CyZooNiC/cyberdeck/photos/P_20210604_110600.jpg

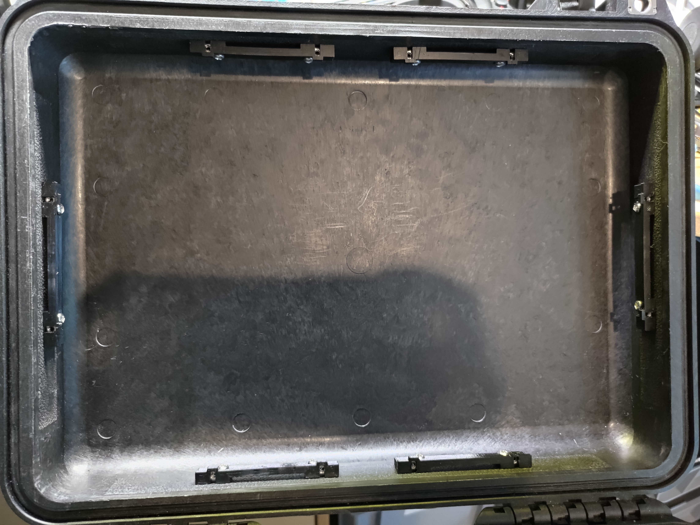
photos/P_20210604_110600.jpg
