CyZooNiC/cyberdeck/photos/P_20210610_104830_-_Copy.jpg

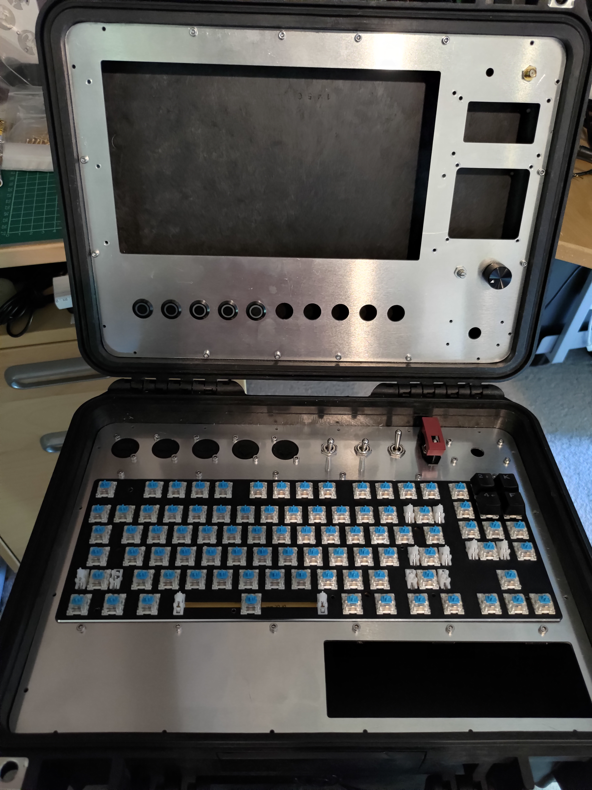
photos/P_20210610_104830_-_Copy.jpg
