CyZooNiC/cyberdeck/photos/P_20211003_194509.jpg

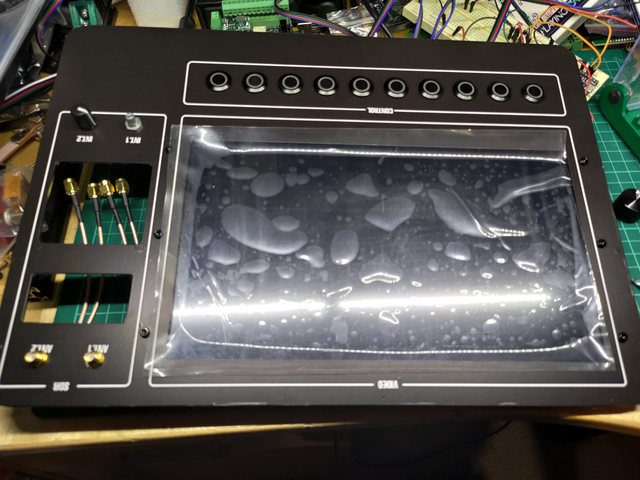
photos/P_20211003_194509.jpg
