CyZooNiC/cyberdeck/photos/P_20220129_154814.jpg

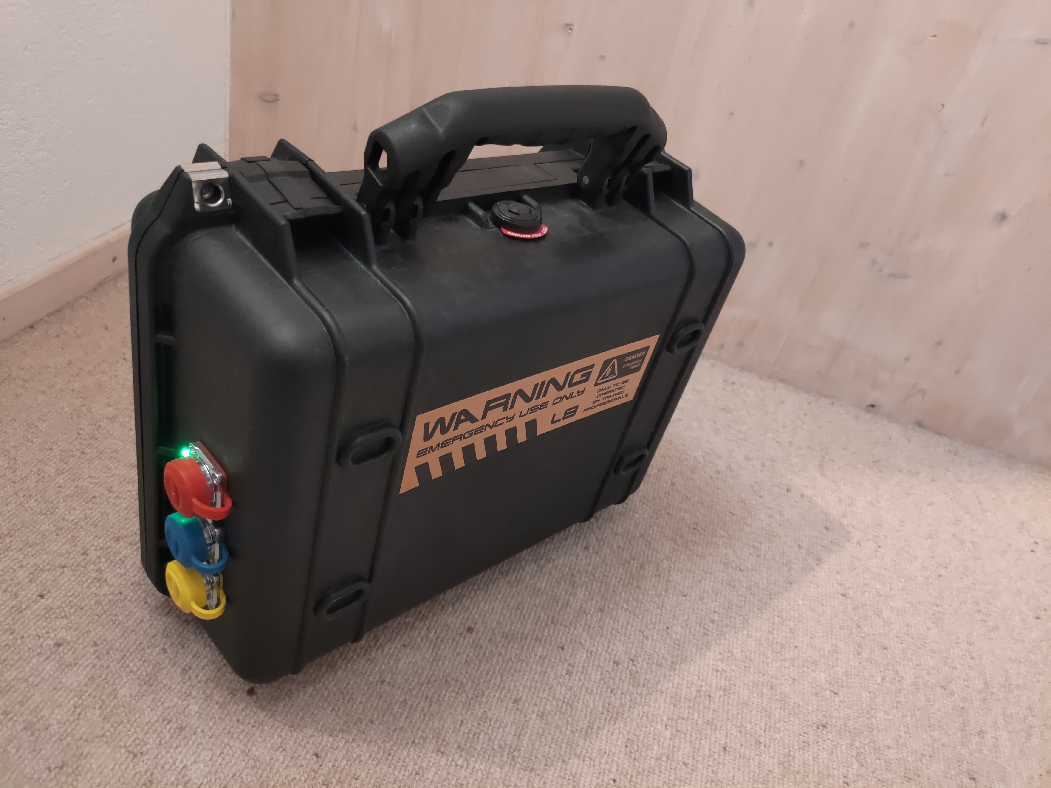
photos/P_20220129_154814.jpg
