CyZooNiC/cyberdeck/photos/P_20220129_154857.jpg

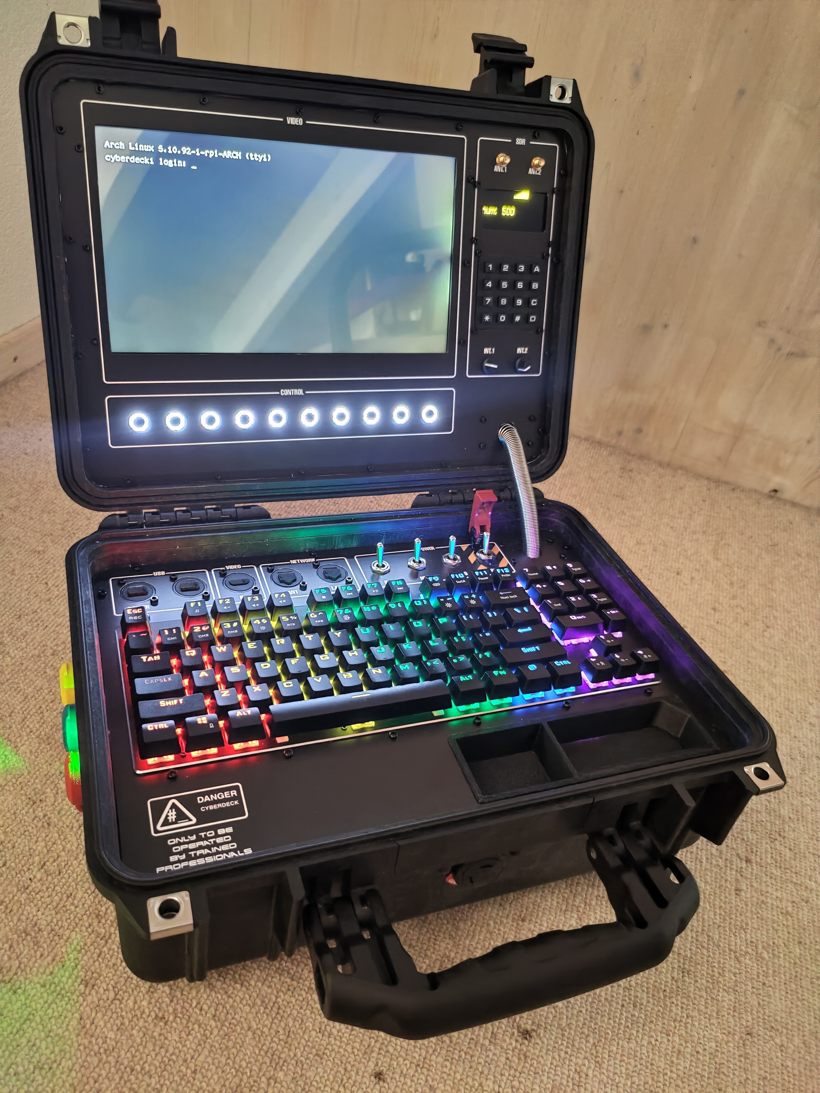
photos/P_20220129_154857.jpg
