CyZooNiC/cyberdeck/photos/P_20220129_154932.jpg

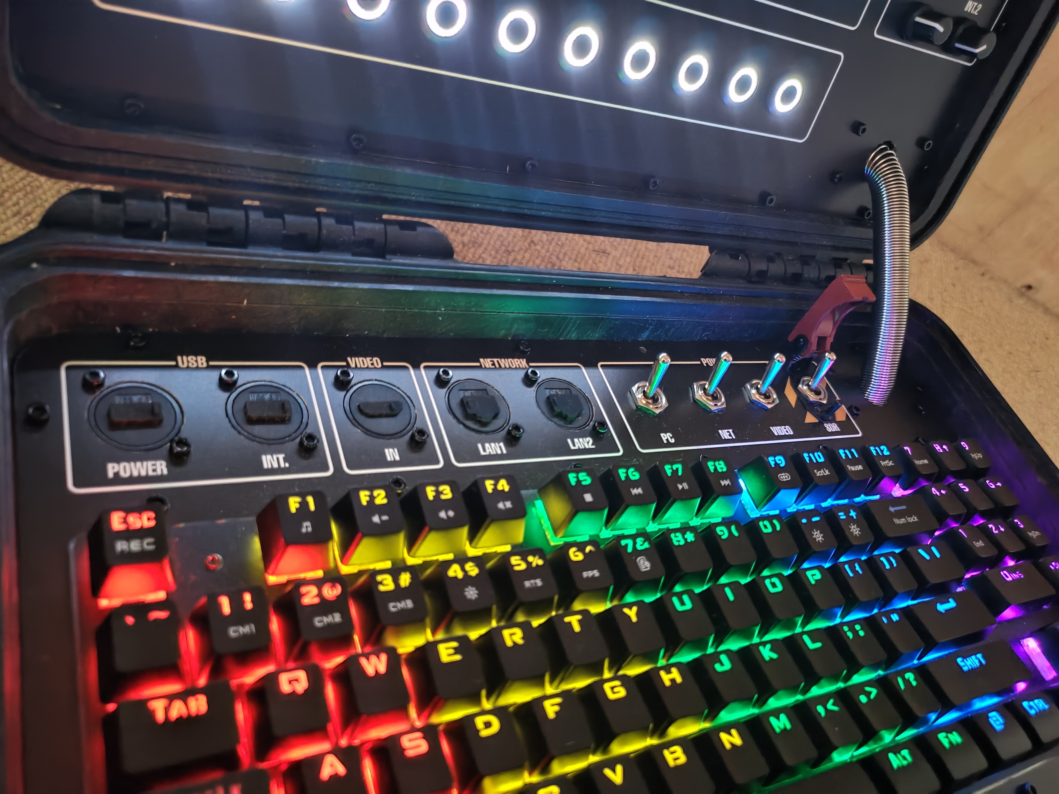
photos/P_20220129_154932.jpg
