CyZooNiC/cyberdeck/photos/P_20220129_154947.jpg

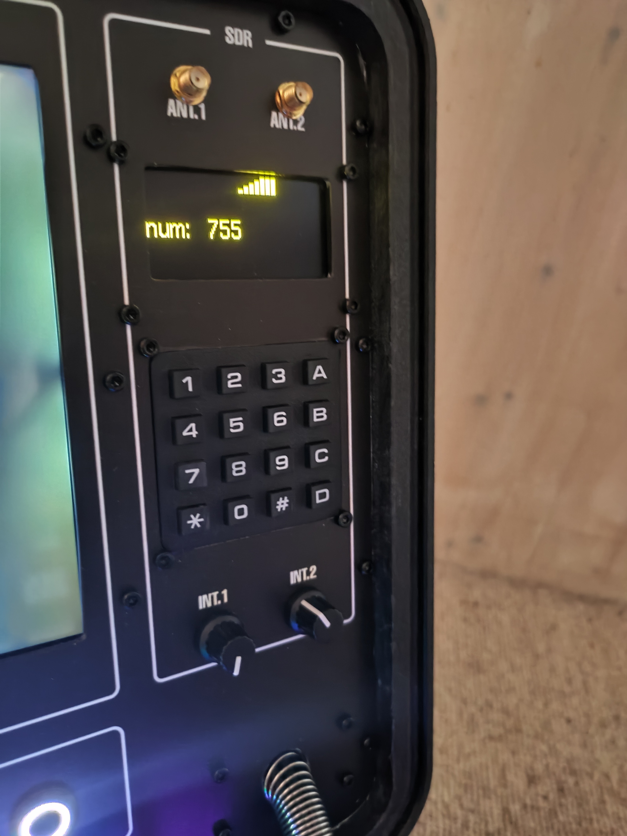
photos/P_20220129_154947.jpg
