CyZooNiC/cyberdeck/photos/P_20220129_155039.jpg

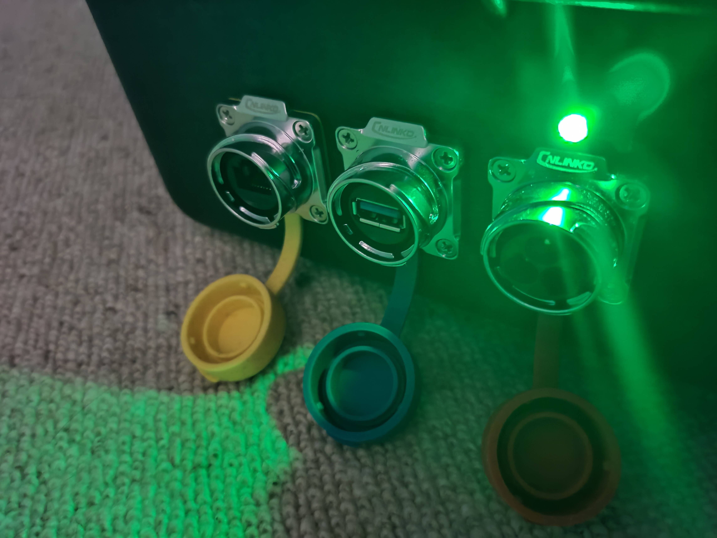
photos/P_20220129_155039.jpg
