CyZooNiC/cyberdeck/photos/P_20220129_155115.jpg

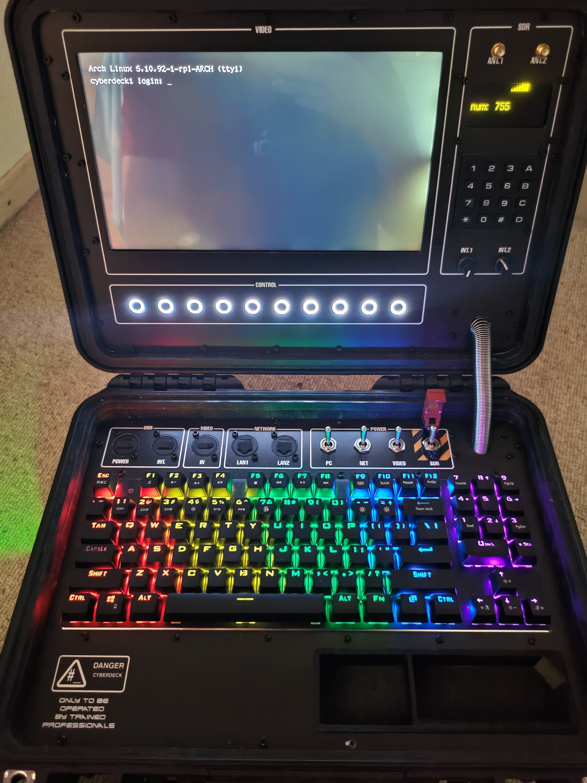
photos/P_20220129_155115.jpg
