CyZooNiC/cyberdeck/photos/P_20220205_175429.jpg

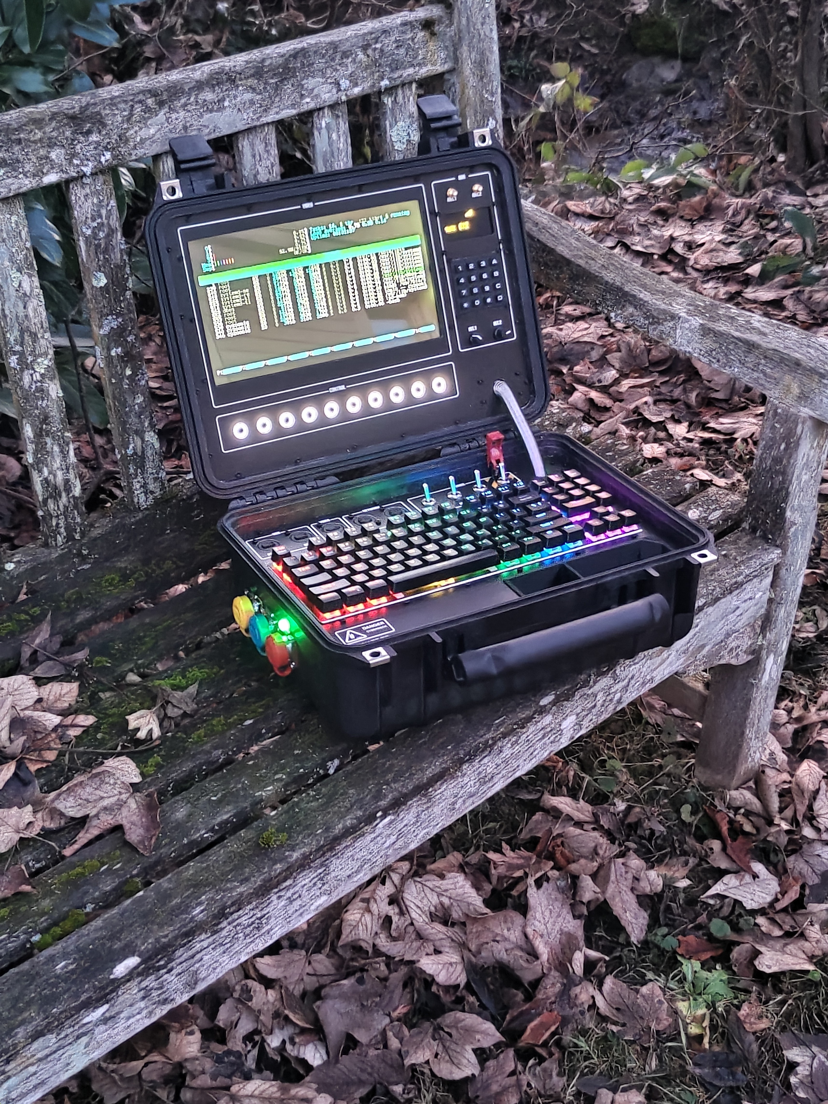
photos/P_20220205_175429.jpg
