CyZooNiC/cyberdeck/photos/P_20220205_175459.jpg

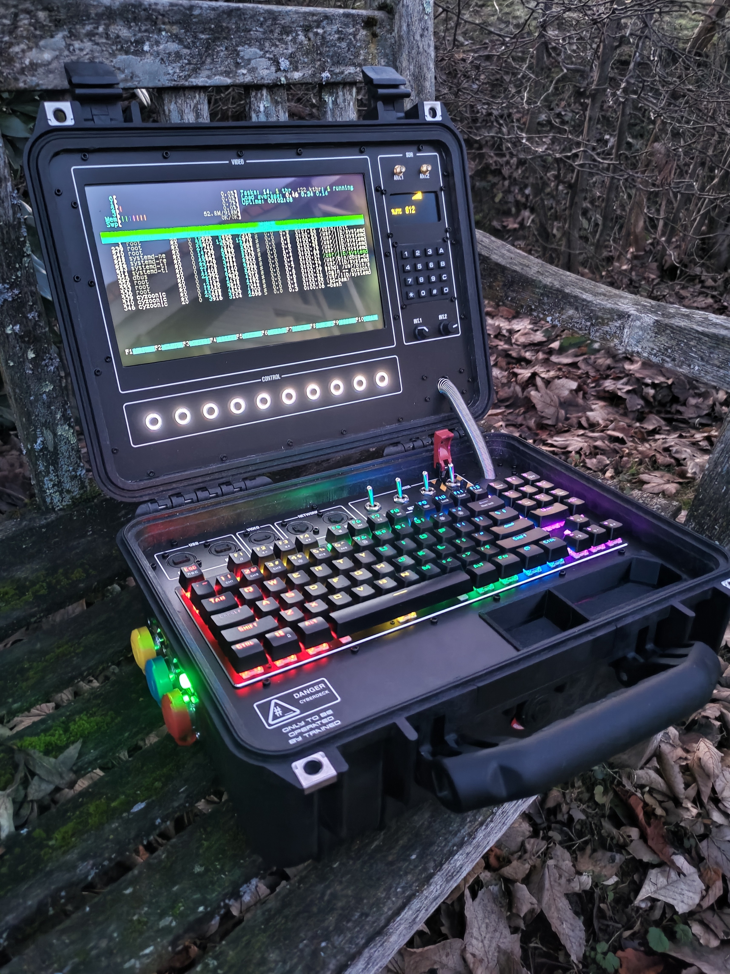
photos/P_20220205_175459.jpg
