CyZooNiC/cyberdeck/photos/P_20220205_175647.jpg

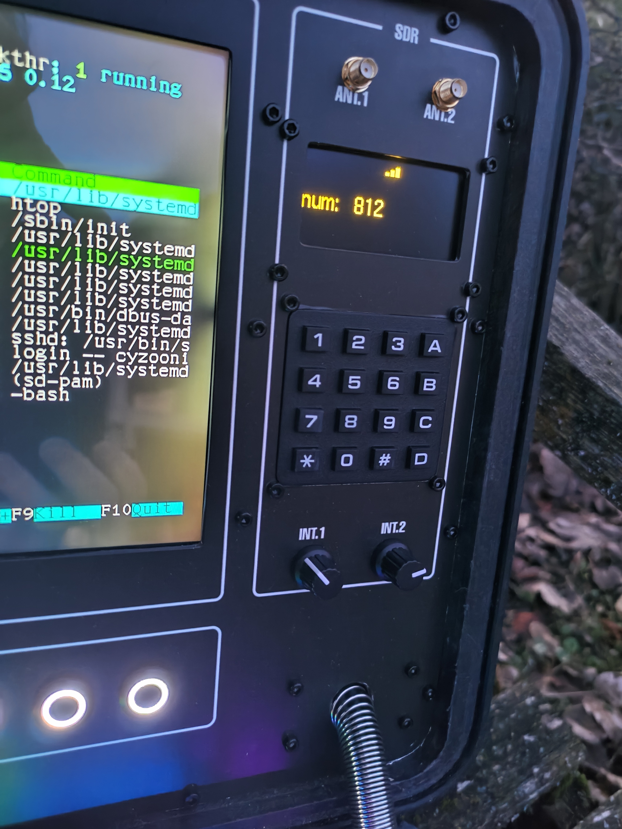
photos/P_20220205_175647.jpg
