CyZooNiC/cyberdeck/photos/P_20220205_175659.jpg

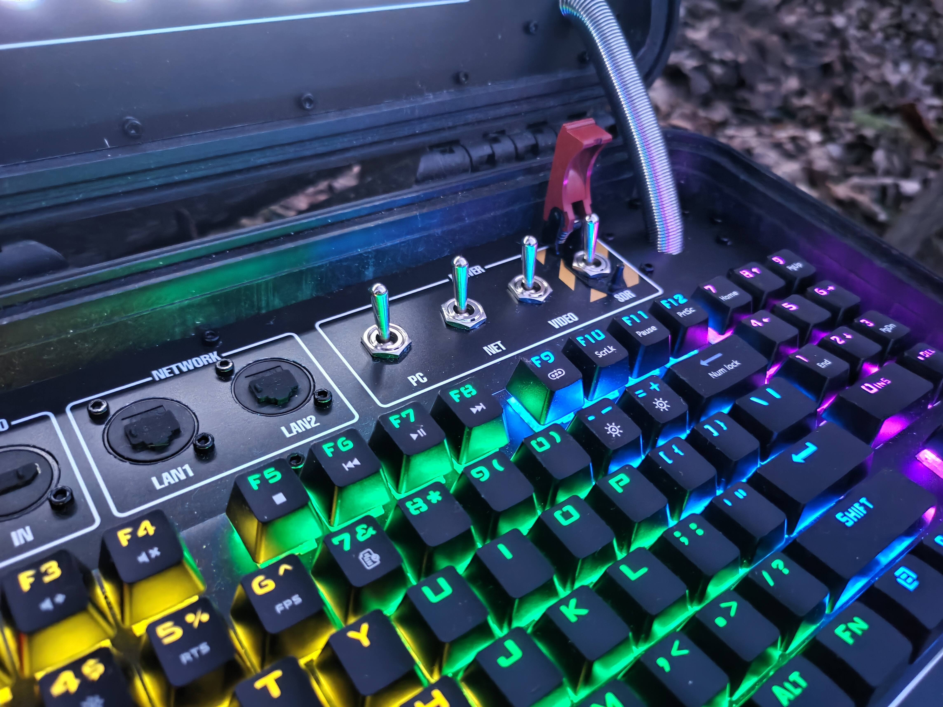
photos/P_20220205_175659.jpg
