CyZooNiC/cyberdeck/photos/P_20220205_175714.jpg

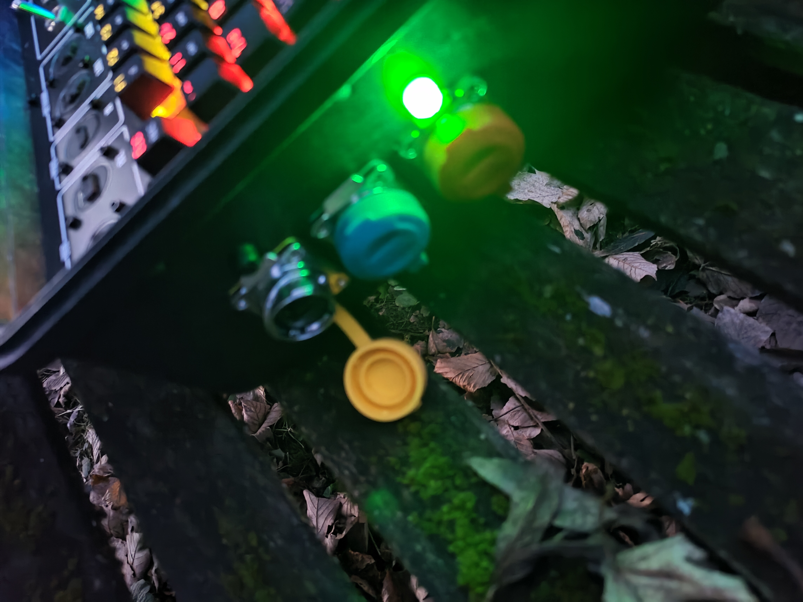
photos/P_20220205_175714.jpg
