CyZooNiC/cyberdeck/photos/P_20220205_175735.jpg

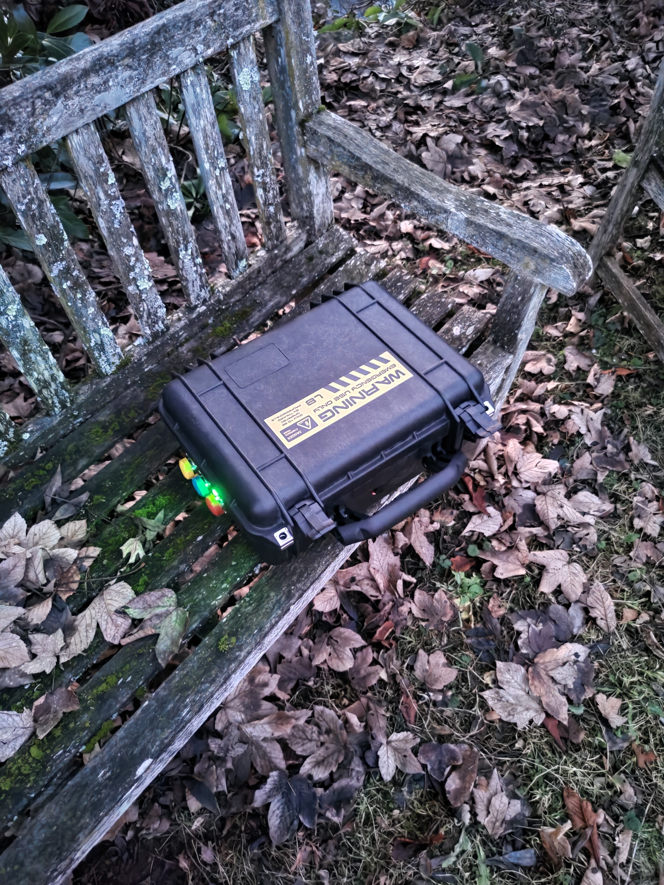
photos/P_20220205_175735.jpg
