CyZooNiC/cyberdeck/photos/P_20220205_175752.jpg

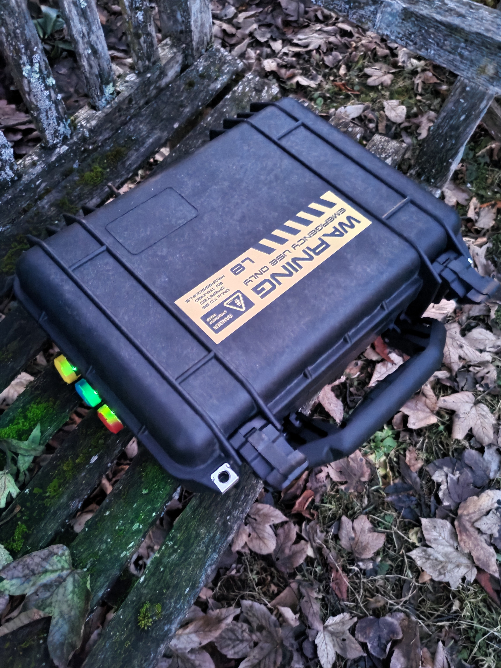
photos/P_20220205_175752.jpg
