CyZooNiC/cyberdeck/photos/P_20220205_175809.jpg

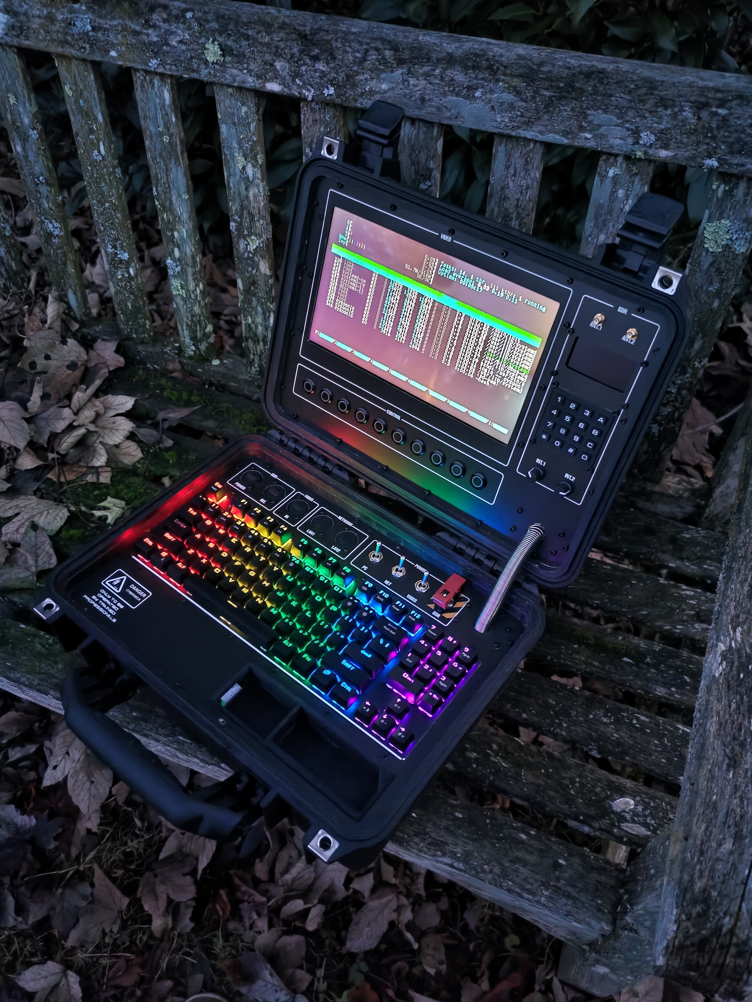
photos/P_20220205_175809.jpg
