CyZooNiC/cyberdeck/photos/P_20220217_164849.jpg

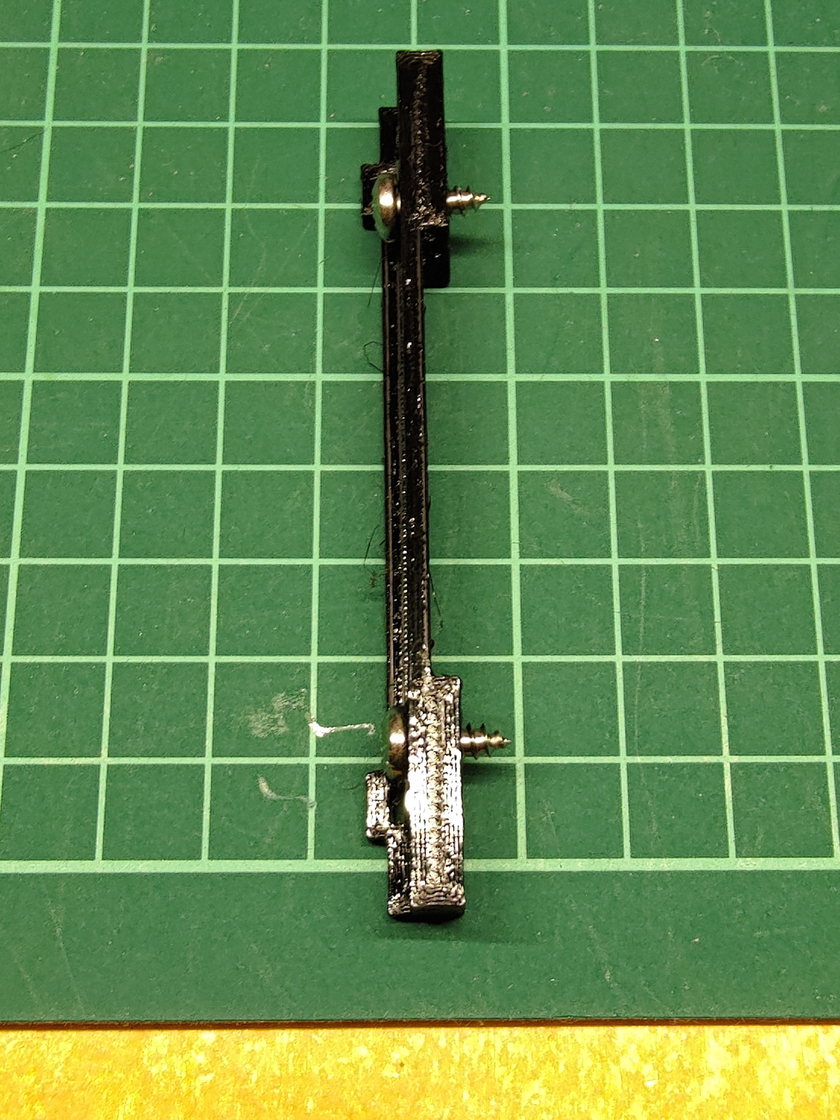
photos/P_20220217_164849.jpg
