CyZooNiC/cyberdeck/photos/P_20220217_164942(1).jpg

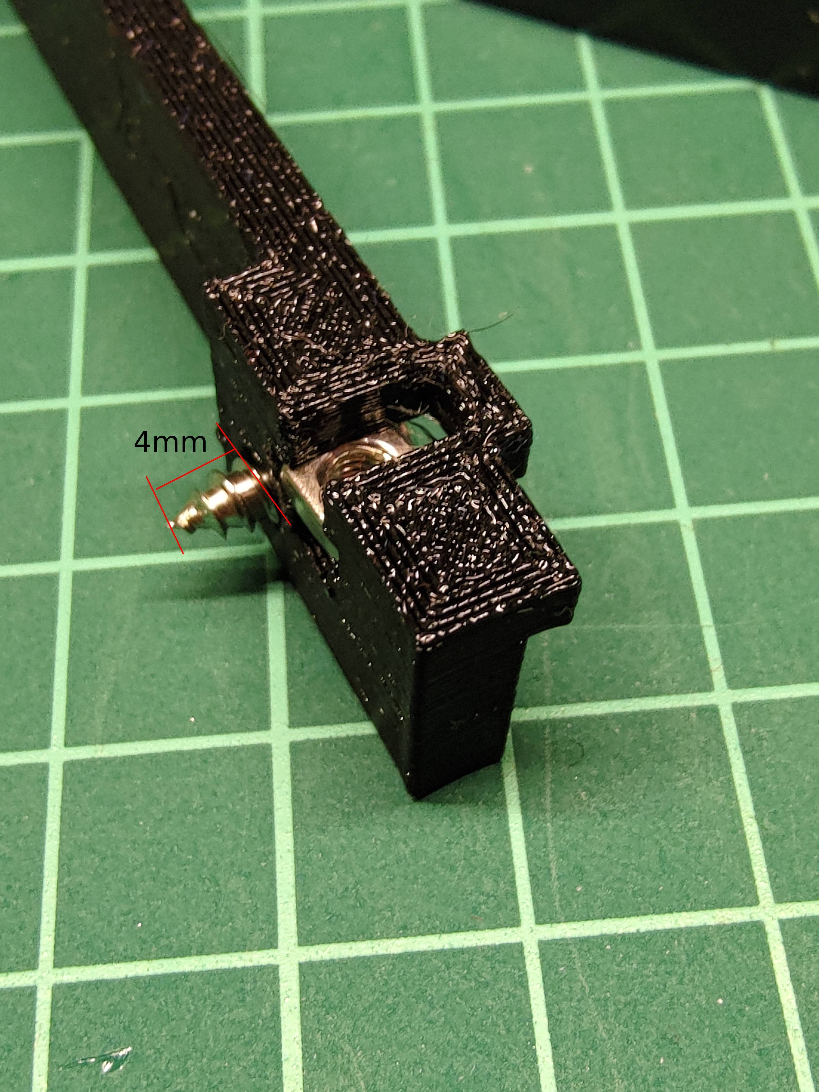
photos/P_20220217_164942(1).jpg
