CyZooNiC/cyberdeck/photos/P_20220217_170358(1).jpg

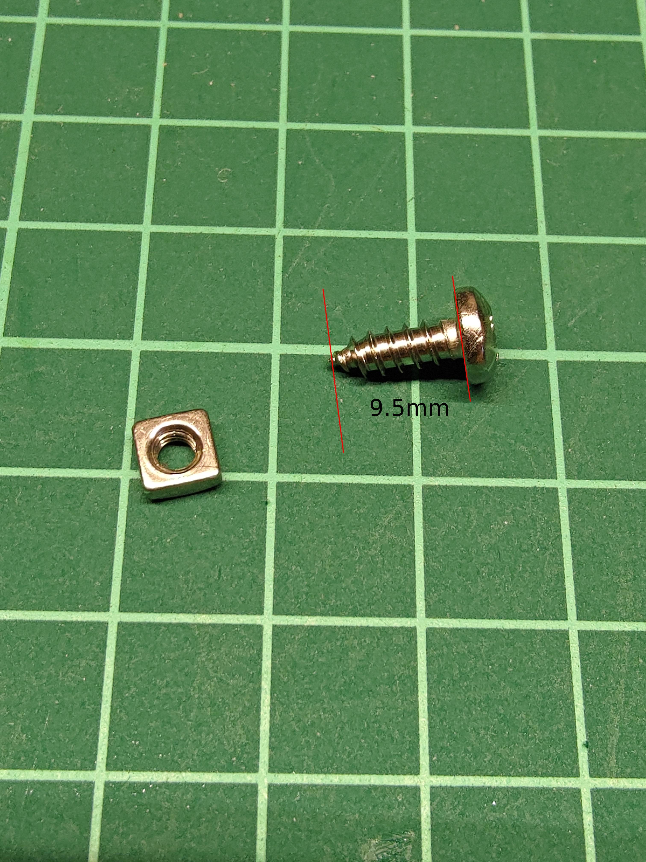
photos/P_20220217_170358(1).jpg
