CyZooNiC/cyberdeck/sdr-pcb/Screenshot_2022-02-05_18-30-27.png

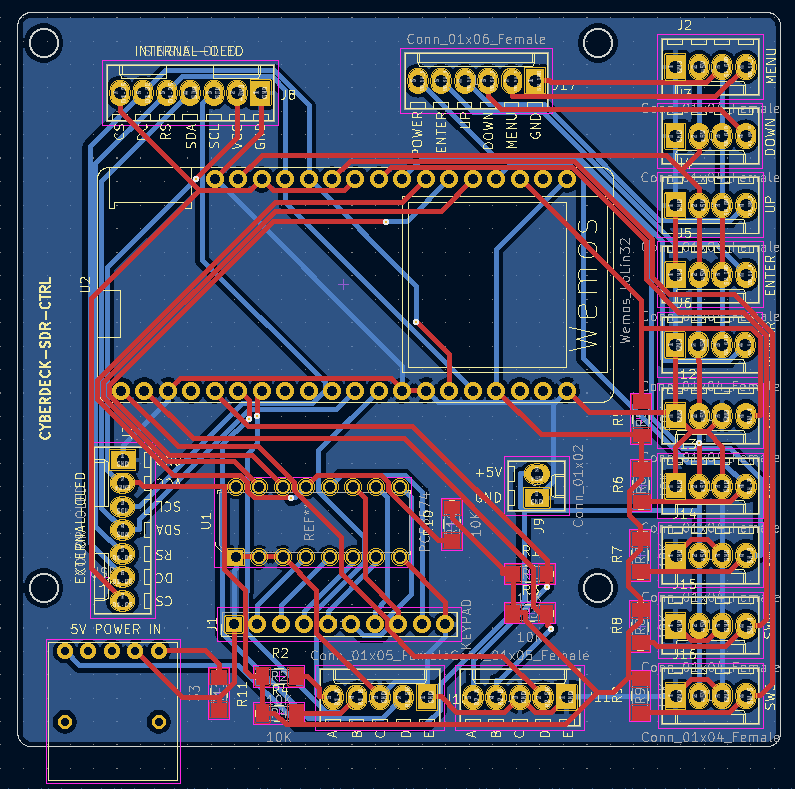
sdr-pcb/Screenshot_2022-02-05_18-30-27.png
