CyZooNiC/cyberdeck/sdr-pcb/Screenshot_2022-02-05_18-31-20.png

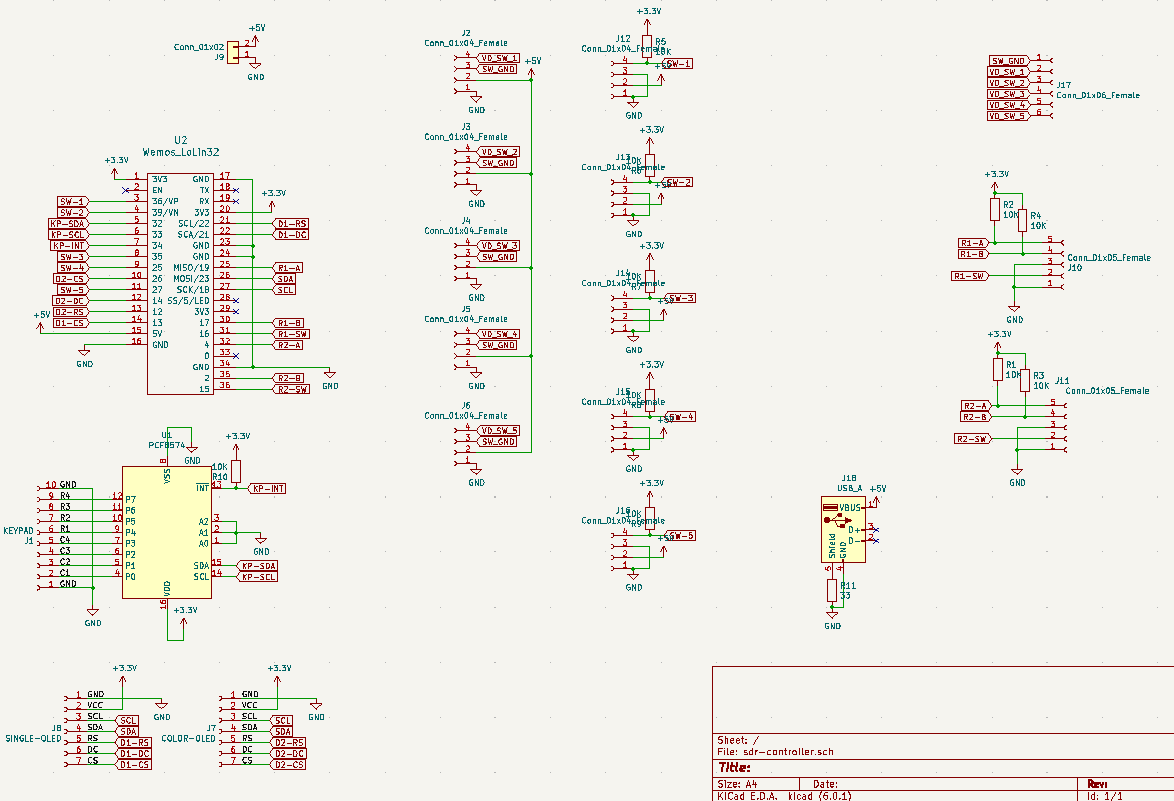
sdr-pcb/Screenshot_2022-02-05_18-31-20.png
