CyZooNiC/cyberdeck/photos/P_20211208_180651_-_Copy.jpg

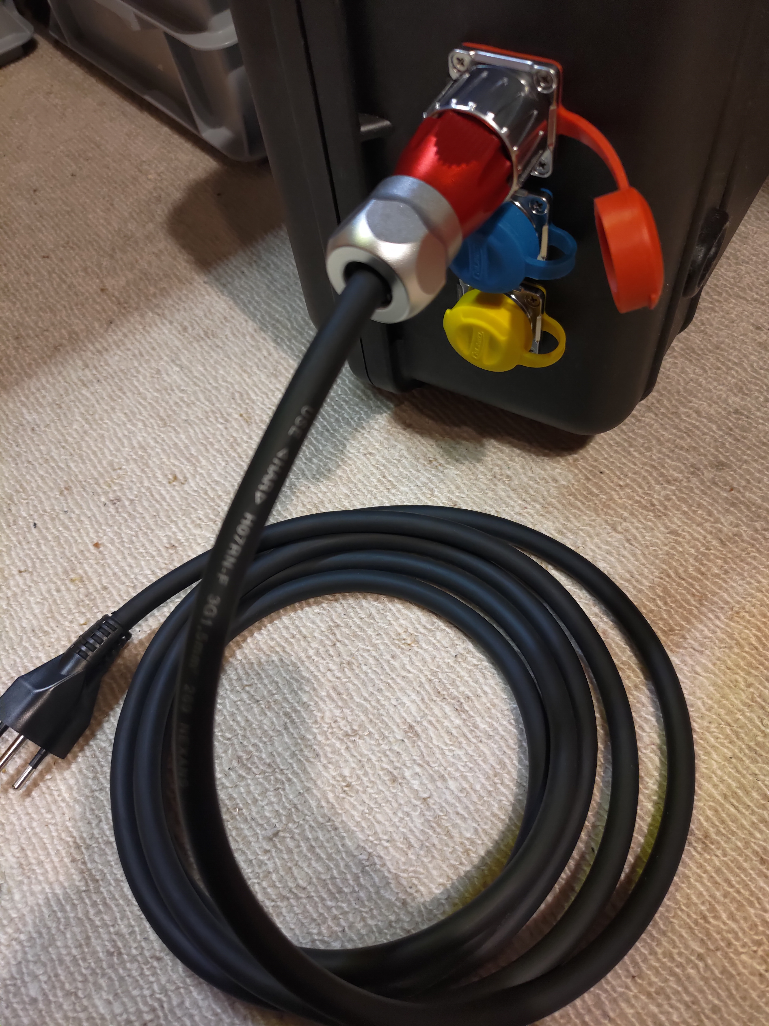
photos/P_20211208_180651_-_Copy.jpg
